brucemack/WARS-Birdhouse/fw/station/packets.h

/* 
 * LoRa Birdhouse Mesh Network Project
 * Wellesley Amateur Radio Society
 * 
 * Copyright (C) 2022 Bruce MacKinnon
 *
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
 * You should have received a copy of the GNU General Public License
 * along with this program.  If not, see <https://www.gnu.org/licenses/>.
 */
#ifndef _packets_h
#define _packets_h

#include <string.h>

#include "Utils.h"
#include "Configuration.h"

const uint8_t PACKET_VERSION = 2;
static const nodeaddr_t BROADCAST_ADDR = 0xffff;

// The top bit indicates whether an ACK is needed
enum MessageType {
    TYPE_UNUSED        = 0,
    // This message is used when a delivery acknowledgment is needed
    TYPE_ACK           = 1,
    // Used to spontaneously 
    TYPE_STATION_ID    = 2,
    // The ping message will be acknowledged at every step along the way
    TYPE_PING_REQ      = 3,
    // Response is acknowledged as well
    TYPE_PING_RESP     = 4,
    // Station engineering data
    TYPE_GETSED_REQ    = 5,
    TYPE_GETSED_RESP   = 6,
    TYPE_SETROUTE      = 10,
    TYPE_GETROUTE_REQ  = 11,
    TYPE_GETROUTE_RESP = 12,
    TYPE_RESET         = 15,
    TYPE_RESET_COUNTERS = 17,
    // Routine text traffic
    TYPE_TEXT          = 32,
    TYPE_ALERT         = 36
};

struct Header {

    uint8_t version;
    uint8_t type;
    uint16_t id;
    char sourceCall[8];
    char finalDestCall[8];
    char originalSourceCall[8];
    nodeaddr_t destAddr;
    nodeaddr_t sourceAddr;
    // Used for multi-hop communication.  This is the node that is 
    // the ultimate destination of a message.
    nodeaddr_t finalDestAddr;
    // Used for multi-hop communication.  This is the node that 
    // originated the message.
    nodeaddr_t originalSourceAddr;

    Header() 
    : version(PACKET_VERSION) 
    {
    }

    /**
     * @brief Constructor that initializes from a binary buffer
     * (most likely one that we just took from the radio).
     * 
     * @param rx_buf 
     */
    Header(const char* rx_buf) {
        memcpy(this, rx_buf, sizeof(Header));
    }

    /**
     * @brief Create a ACK message for a message that we received.
     * 
     * @param rx_packet 
     * @param myCall 
     * @param myAddr 
     */
    void setupAckFor(const Header& rx_packet, const Configuration& config) {
        version = PACKET_VERSION;
        type = TYPE_ACK;
        id = rx_packet.id;
        // Address stuff
        sourceAddr = config.getAddr();
        destAddr = rx_packet.sourceAddr;
        // Echo back the original stuff
        originalSourceAddr = rx_packet.originalSourceAddr;
        finalDestAddr = rx_packet.finalDestAddr;
        CallSign myCall = config.getCall();
        myCall.writeTo(sourceCall);

        // Echo back the original stuff
        memcpy(finalDestCall, rx_packet.finalDestCall, 8);
        memcpy(originalSourceCall, rx_packet.originalSourceCall, 8);
    }

    /**
     * @brief Fills in this header with the information needed to 
     * generate a response to the request header.  Deals with 
     * updating the callsigns and addresses.
     * 
     * @param req_header 
     * @param myCall 
     * @param myAddr 
     * @param packetType 
     */
    void setupResponseFor(const Header& reqHeader, const Configuration& config,
        uint8_t respType, uint16_t respId, nodeaddr_t respDestAddr) {
        
        version = PACKET_VERSION;
        type = respType;
        id = respId;
        // Address stuff
        sourceAddr = config.getAddr();
        destAddr = respDestAddr;
        originalSourceAddr = config.getAddr();
        // SWAP 
        finalDestAddr = reqHeader.originalSourceAddr;
        // Call stuff
        CallSign myCall = config.getCall();
        myCall.writeTo(sourceCall);
        myCall.writeTo(originalSourceCall);
        // SWAP
        memcpy(finalDestCall, reqHeader.originalSourceCall, 8);
    }

    void setup(const Configuration& config,
        uint8_t packetType, uint16_t packetId, nodeaddr_t packetDestAddr, nodeaddr_t packetFinalDestAddr) {        
        version = PACKET_VERSION;
        type = packetType;
        id = packetId;
        // Address stuff
        sourceAddr = config.getAddr();
        originalSourceAddr = config.getAddr();
        destAddr = packetDestAddr;
        finalDestAddr = packetFinalDestAddr;
        // Call stuff
        CallSign myCall = config.getCall();
        myCall.writeTo(sourceCall);
        myCall.writeTo(originalSourceCall);
    }

    bool isAck() const {
        return (type == TYPE_ACK);
    }

    bool isAckRequired() const {
        return !(type == TYPE_ACK || type == TYPE_STATION_ID) && 
          (destAddr != BROADCAST_ADDR);
    }

    bool isResponseRequired() const {
        return (type == TYPE_PING_REQ || type == TYPE_GETSED_REQ ||
          type == TYPE_GETROUTE_REQ);
    }

    uint8_t getPacketVersion() const {
        return version;
    }
    
    uint8_t getType() const {
        return type;
    }

    void setType(uint8_t t) {
        type = t;
    }

    uint16_t getId() const {
        return id;
    }

    void setId(uint16_t i) {
        id = i;
    }

    nodeaddr_t getSourceAddr() const {
        return sourceAddr;
    }

    void setSourceAddr(nodeaddr_t addr) {
        sourceAddr = addr;
    }

    nodeaddr_t getDestAddr() const {
        return destAddr;
    }

    void setDestAddr(nodeaddr_t addr) {
        destAddr = addr;
    }

    nodeaddr_t getOriginalSourceAddr() const {
        return originalSourceAddr; 
    }

    void setOriginalSourceAddr(nodeaddr_t addr) {
        originalSourceAddr = addr;
    }

    nodeaddr_t getFinalDestAddr() const {
        return finalDestAddr;
    }

    void setFinalDestAddr(nodeaddr_t addr) {
        finalDestAddr = addr;
    }

    void setSourceCall(const CallSign& call) {
        call.writeTo(sourceCall);
    }

    CallSign getSourceCall() const {
        CallSign result;
        result.readFrom(sourceCall);
        return result;
    }

    void setOriginalSourceCall(const CallSign& call) {
        call.writeTo(originalSourceCall);
    }

    CallSign getOriginalSourceCall() const {
        CallSign result;
        result.readFrom(originalSourceCall);
        return result;
    }

    void setFinalDestCall(const CallSign& call) {
        call.writeTo(finalDestCall);
    }

    bool isRelevant(nodeaddr_t myAddr) const {
        return destAddr == myAddr || destAddr == BROADCAST_ADDR;
    }
};

static const unsigned int MAX_PAYLOAD_SIZE = 128 - sizeof(Header);

struct Packet {
    Header header;
    uint8_t payload[MAX_PAYLOAD_SIZE];
};

struct SadRespPayload {
  uint16_t version;
  uint16_t batteryMv;
  uint16_t panelMv;
  uint32_t uptimeSeconds;
  uint32_t time;
  uint16_t bootCount;
  uint16_t sleepCount;
  // Message processing diagnostic counters
  uint16_t rxPacketCount;
  uint16_t badRxPacketCount;
  uint16_t badRouteCount;
  int16_t temp;
  int16_t humidity;
  uint16_t deviceClass;
  uint16_t deviceRevision;
  uint16_t wrongNodeRxCount;
  // RSSI of the last hop (i.e. the link to the target node)
  int16_t lastHopRssi;
  int16_t UNUSED0;
  int16_t UNISED1;
  int16_t UNUSED2;
  int16_t UNISED3;
};

struct SetRouteReqPayload {
  uint32_t passcode;
  nodeaddr_t targetAddr;
  nodeaddr_t nextHopAddr;  
};

struct GetRouteReqPayload {
  nodeaddr_t targetAddr;
};

struct GetRouteRespPayload {
  nodeaddr_t targetAddr;
  nodeaddr_t nextHopAddr;  
  uint16_t rxPacketCount;  
  uint16_t txPacketCount;  
};

struct ResetReqPayload {
  uint32_t passcode;
};

#endif
