brucemack/WARS-Birdhouse/fw/station/spi_utils.cpp

/* 
 * LoRa Birdhouse Mesh Network Project
 * Wellesley Amateur Radio Society
 * 
 * Copyright (C) 2022 Bruce MacKinnon
 *
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
 * You should have received a copy of the GNU General Public License
 * along with this program.  If not, see <https://www.gnu.org/licenses/>.
 */
#include <Arduino.h>
#include "spi_utils.h"

#define SS_PIN    5

static SPISettings spi_settings(1000000, MSBFIRST, SPI_MODE0);

void spi_setup() {
  // SPI slave select configuration
  pinMode(SS_PIN, OUTPUT);
  digitalWrite(SS_PIN, HIGH);
  delay(100);
  SPI.begin();
}

uint8_t spi_read(uint8_t reg) {
  SPI.beginTransaction(spi_settings);
  // Slave Select
  digitalWrite(SS_PIN, LOW);
  // Send the address with the write mask off
  SPI.transfer(reg & ~0x80); 
  // The written value is ignored, reg value is read
  uint8_t val = SPI.transfer(0); 
  // Slave deselect
  digitalWrite(SS_PIN, HIGH);
  SPI.endTransaction();
  return val;
}

void spi_read_multi(uint8_t reg, uint8_t* buf, uint8_t len) {
  SPI.beginTransaction(spi_settings);
  // Slave Select
  digitalWrite(SS_PIN, LOW);
  // Send the address with the write mask off
  SPI.transfer(reg & ~0x80); 
  while (len--) {
    // The written value is ignored, reg value is read
    *buf = SPI.transfer(0); 
    buf++;
  }
  // Slave deselect
  digitalWrite(SS_PIN, HIGH);
  SPI.endTransaction();
}

// Writes one byte to SPI.  Returns whatever comes back during the transfer.
//
// NOTE: From RFM95W datasheet (pg 76):
//
// During the write access, the byte transferred from the slave to the master on the MISO line 
// is the value of the written register before the write operation.
//
uint8_t spi_write(uint8_t reg, uint8_t val) {
  SPI.beginTransaction(spi_settings);
  // Slave Select
  digitalWrite(SS_PIN, LOW);
  // Send the address with the write mask on. 
  SPI.transfer(reg | 0x80);
  // Send the data, capturing the original value 
  uint8_t orig_val = SPI.transfer(val); 
  // Slave deselect
  digitalWrite(SS_PIN, HIGH);
  SPI.endTransaction();
  return orig_val;
}

uint8_t spi_write_multi(uint8_t reg, uint8_t* buf, uint8_t len) {
  SPI.beginTransaction(spi_settings);
  // Slave Select
  digitalWrite(SS_PIN, LOW);
  // Send the address with the write mask on
  uint8_t stat = SPI.transfer(reg | 0x80); 
  // Transfer each byte individually
  while (len--) {
    SPI.transfer(*buf);
    buf++;
  }
  // Slave deselect
  digitalWrite(SS_PIN, HIGH);
  SPI.endTransaction();
  return stat;
}
